rayan4444/cleaning_robot_controller/ui_board/layout.PNG

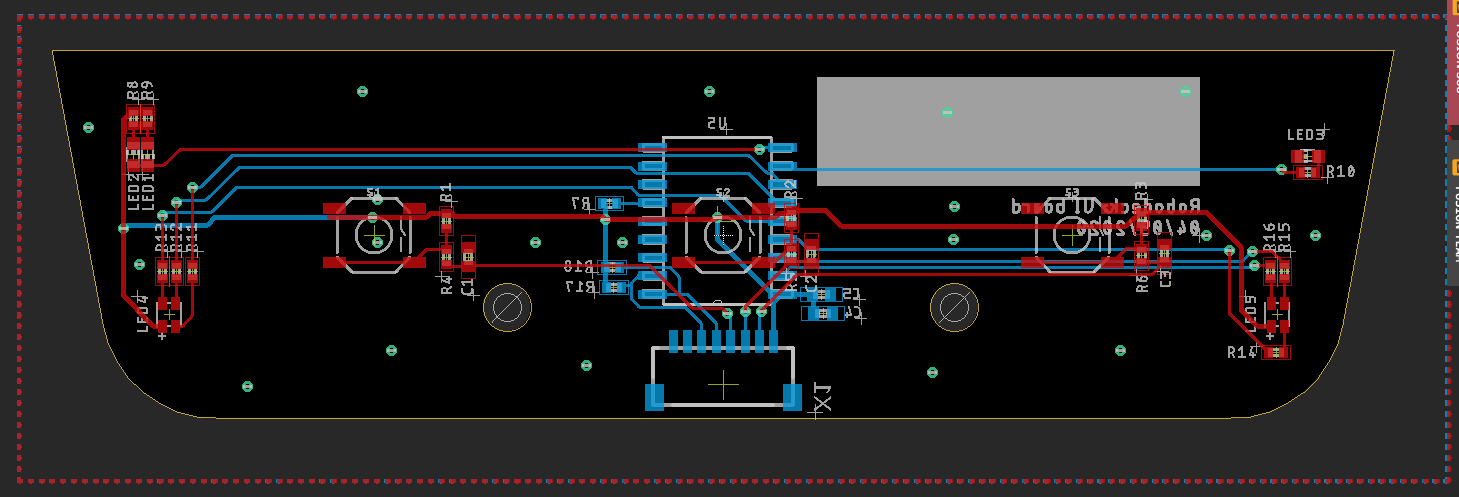
ui_board/layout.PNG
